sigmenx/IPADRESCREEN_IPAD3_4/tmp/04.jpg

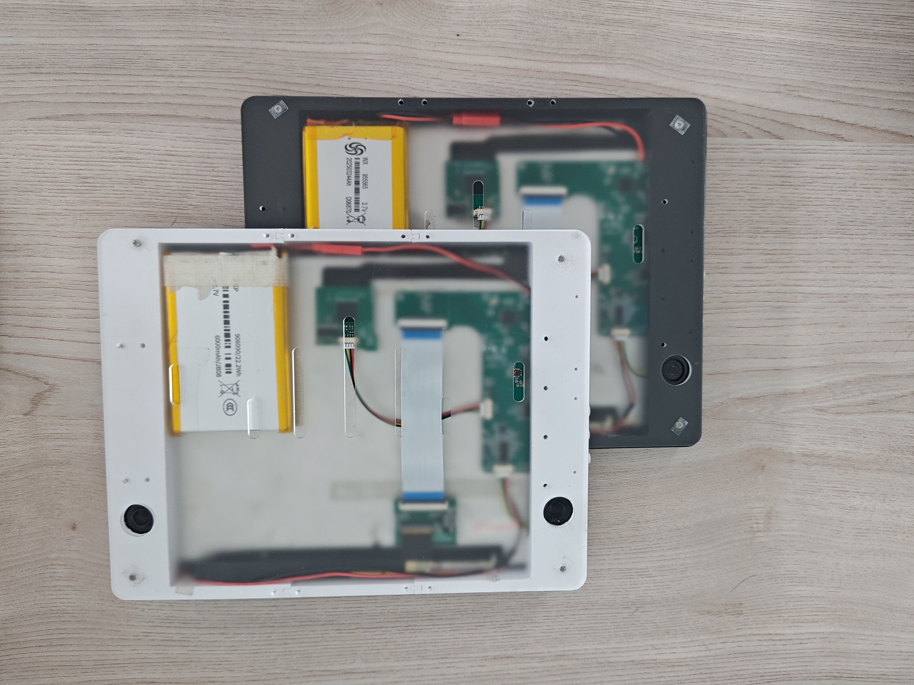
tmp/04.jpg
